IDMIL/EnchantiTouch/firmware/tsticktouch_firmware/images/kit_connection.jpg

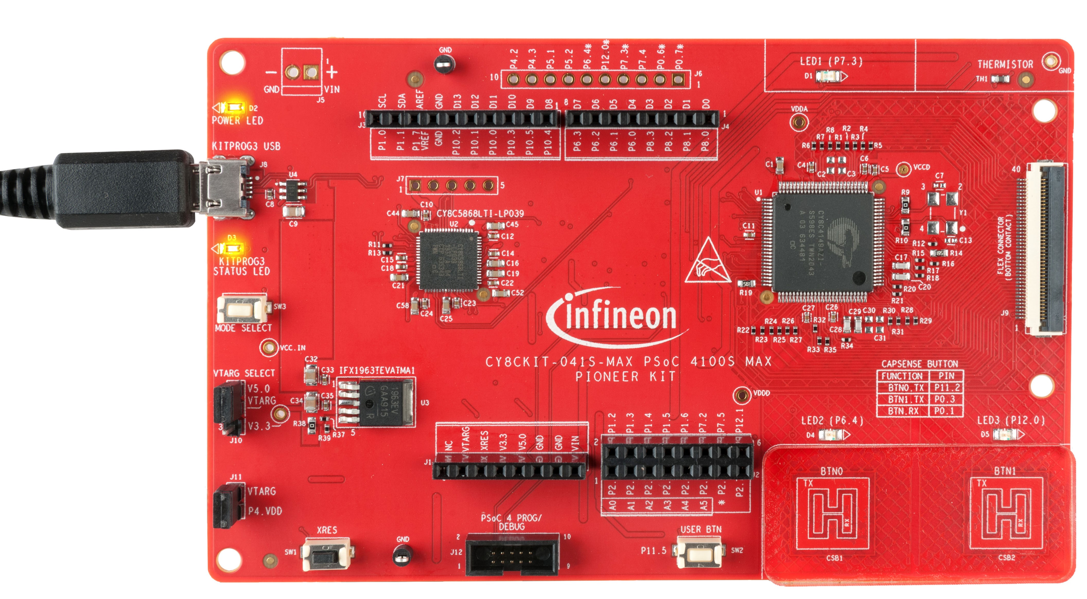
firmware/tsticktouch_firmware/images/kit_connection.jpg
