IDMIL/EnchantiTouch/firmware/tsticktouch_firmware/images/advanced-filter-settings.png

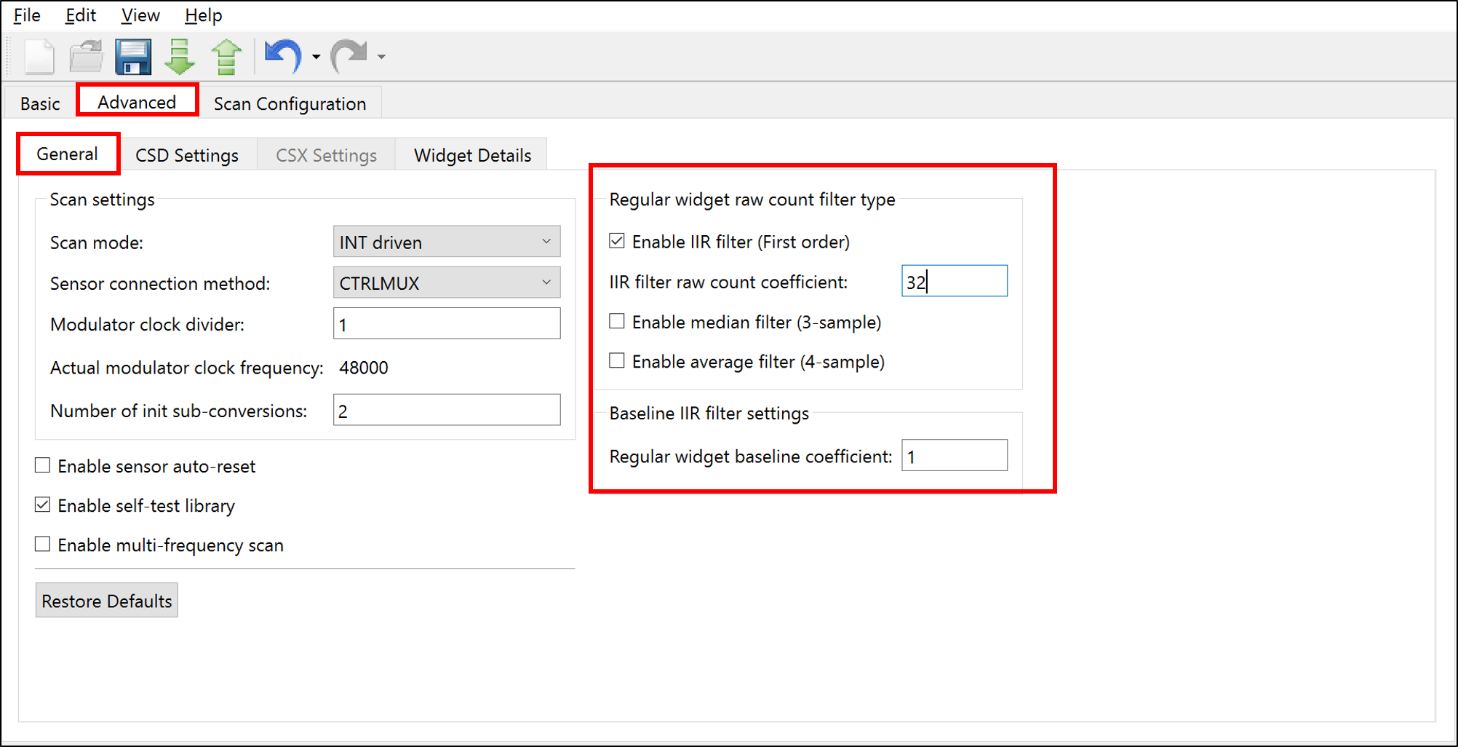
firmware/tsticktouch_firmware/images/advanced-filter-settings.png
