IDMIL/EnchantiTouch/firmware/tsticktouch_firmware/images/advanced-general-settings.png

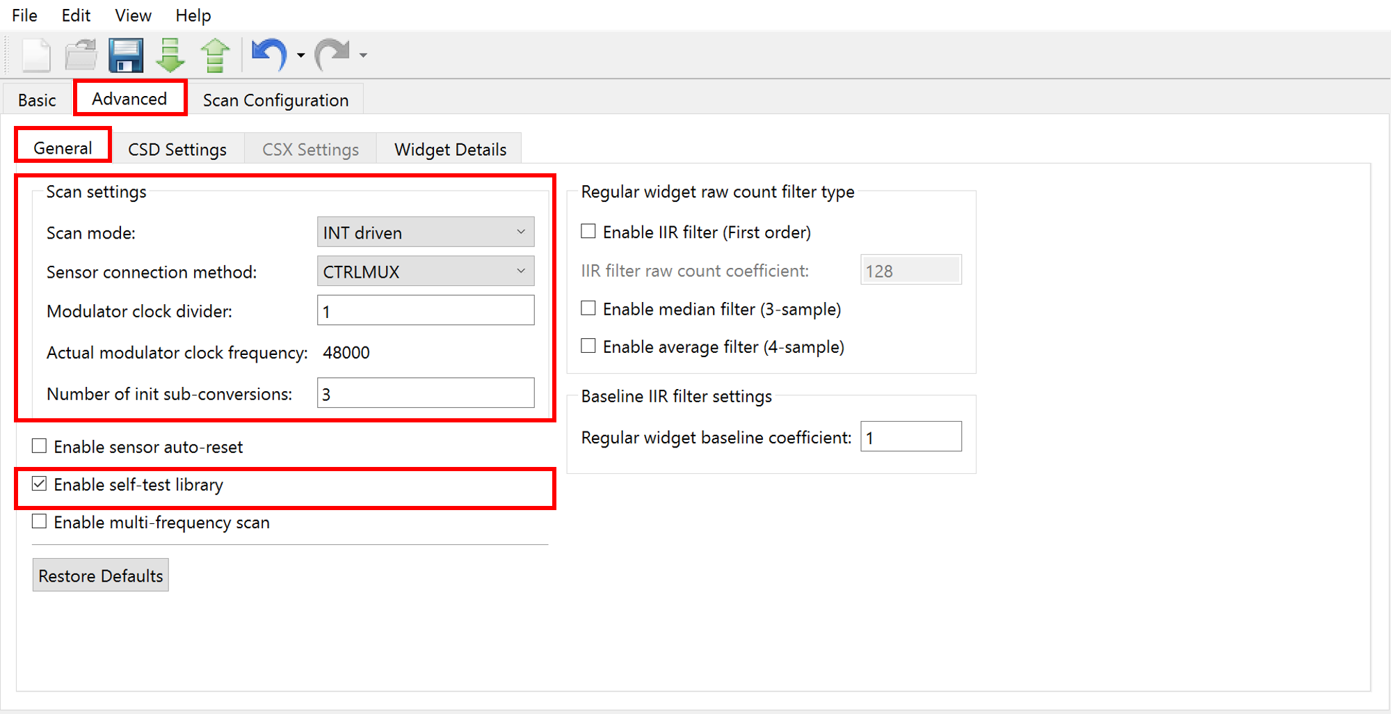
firmware/tsticktouch_firmware/images/advanced-general-settings.png
