IDMIL/EnchantiTouch/firmware/tsticktouch_firmware/images/advanced-widget-settings.png

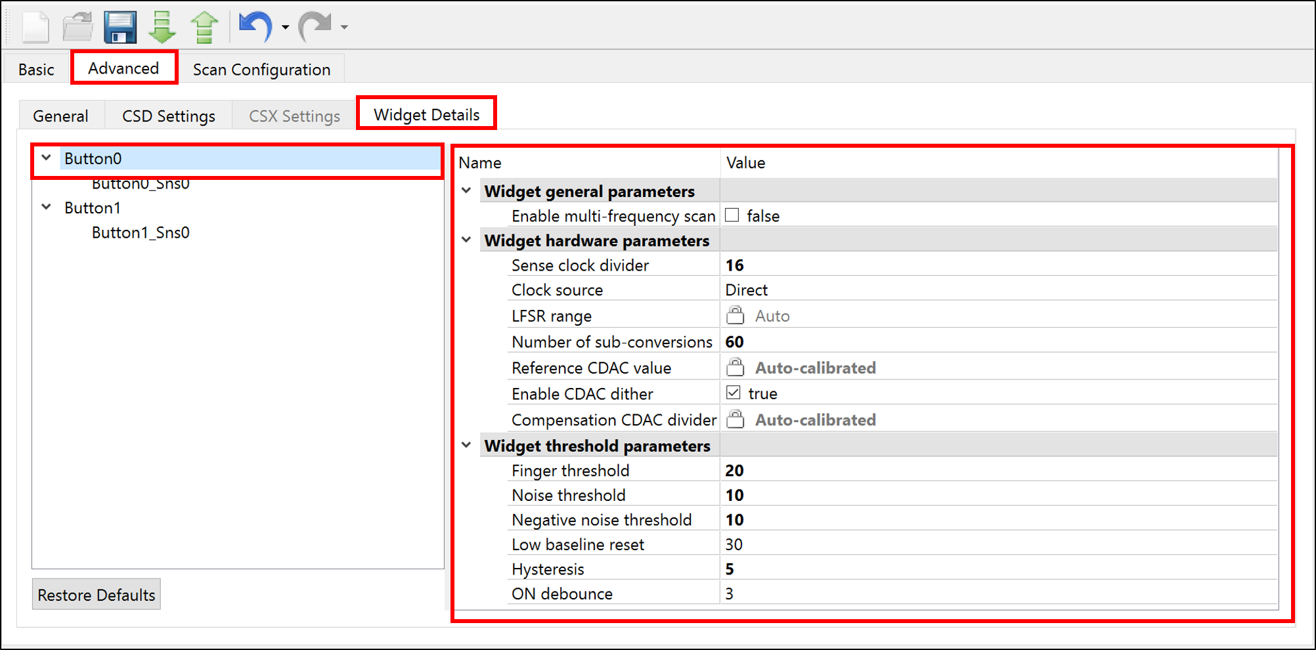
firmware/tsticktouch_firmware/images/advanced-widget-settings.png
