IDMIL/EnchantiTouch/firmware/tsticktouch_firmware/images/basic-csd-settings.png

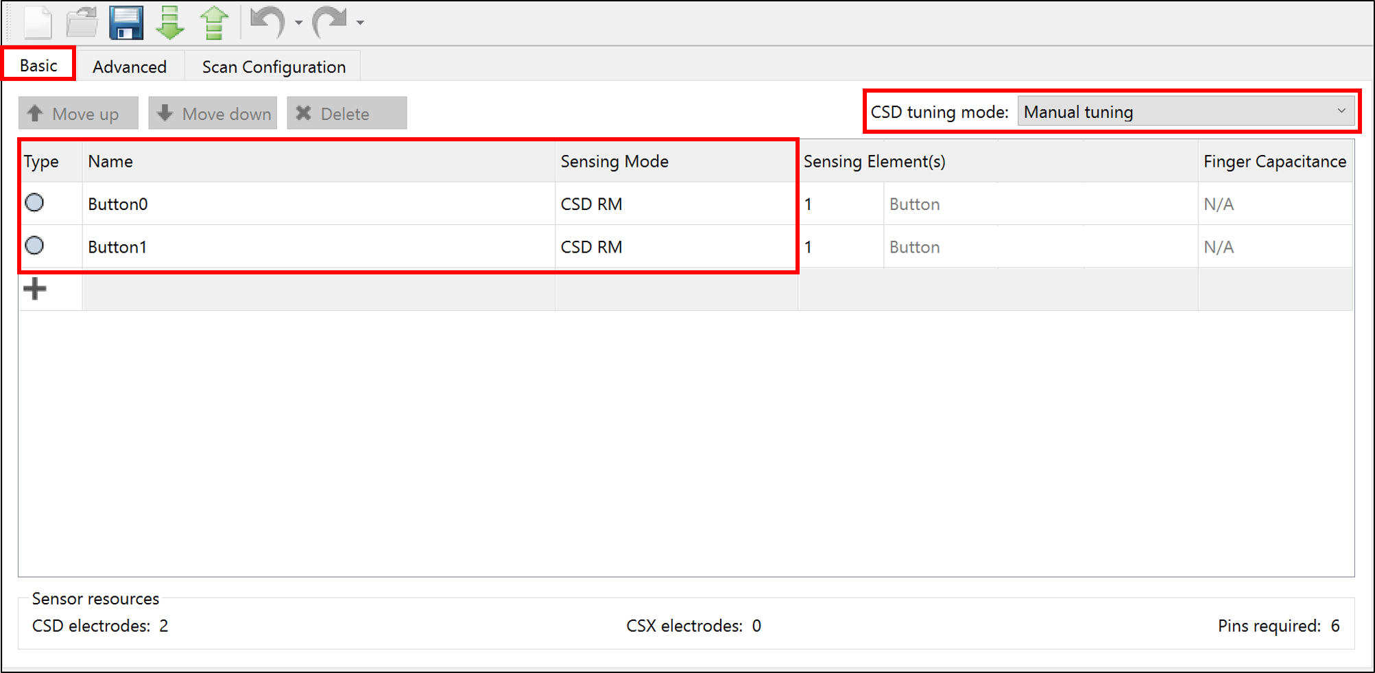
firmware/tsticktouch_firmware/images/basic-csd-settings.png
