IDMIL/EnchantiTouch/firmware/tsticktouch_firmware/images/csdrm-waveform.png

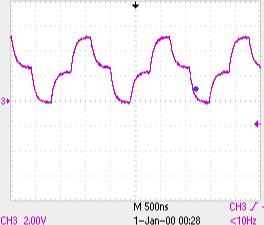
firmware/tsticktouch_firmware/images/csdrm-waveform.png
