IDMIL/EnchantiTouch/firmware/tsticktouch_firmware/images/csdrm-waveform_improper.png

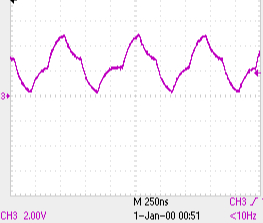
firmware/tsticktouch_firmware/images/csdrm-waveform_improper.png
