IDMIL/EnchantiTouch/firmware/tsticktouch_firmware/images/device-configurator.png

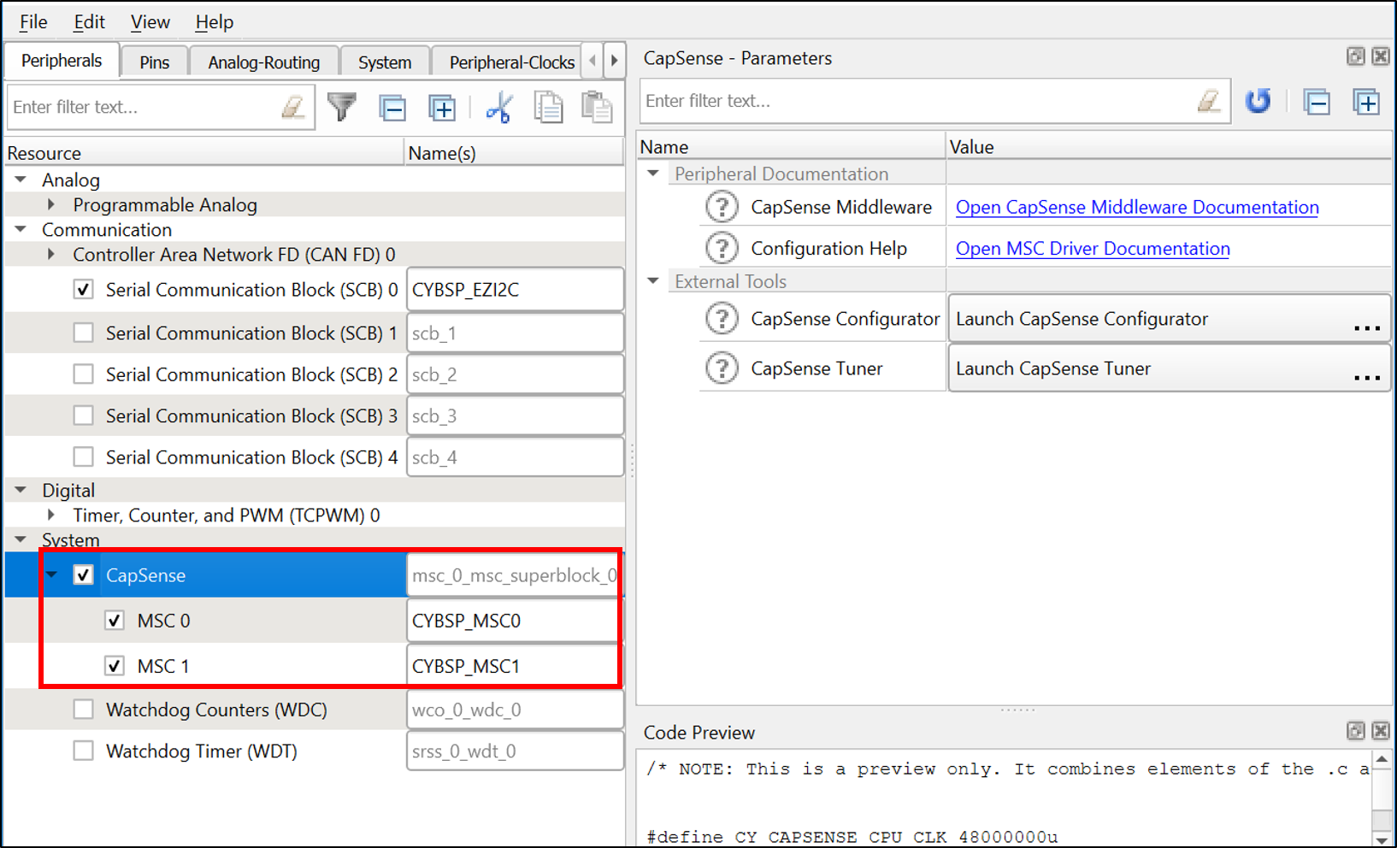
firmware/tsticktouch_firmware/images/device-configurator.png
