IDMIL/EnchantiTouch/firmware/tsticktouch_firmware/images/ezi2c-config.png

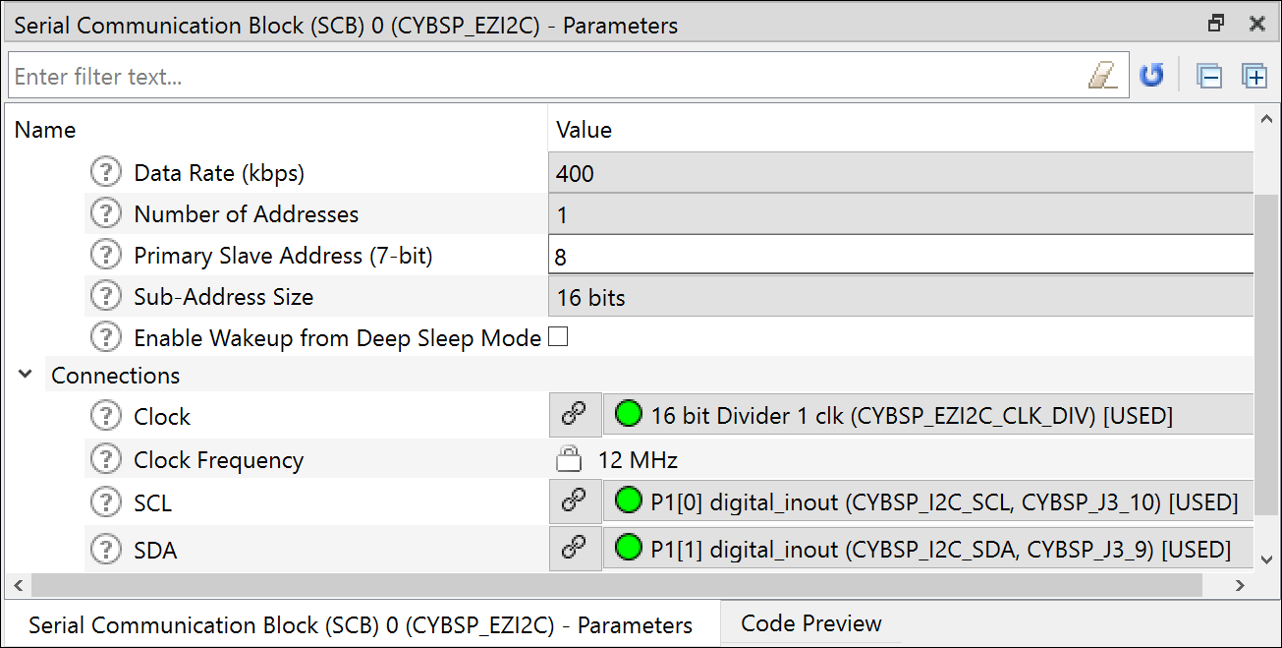
firmware/tsticktouch_firmware/images/ezi2c-config.png
