IDMIL/EnchantiTouch/firmware/tsticktouch_firmware/images/firmware-flowchart.png

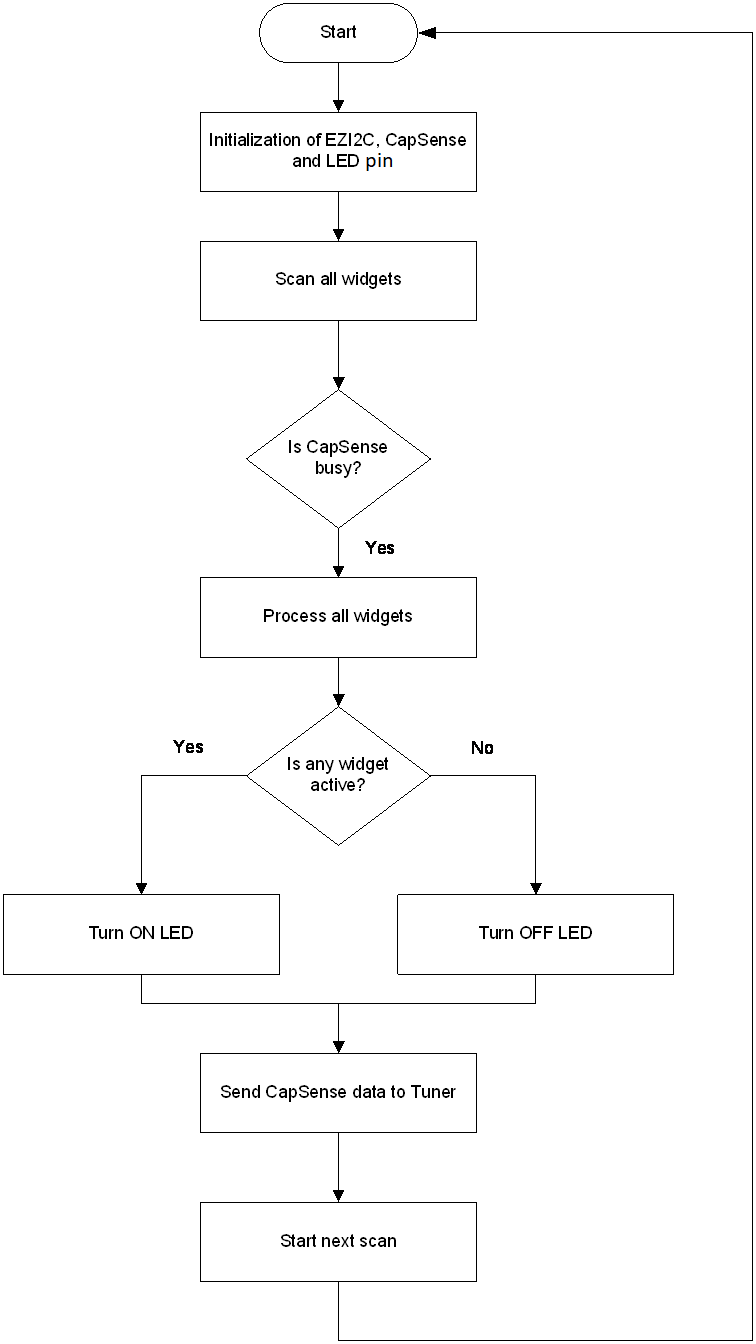
firmware/tsticktouch_firmware/images/firmware-flowchart.png
