IDMIL/EnchantiTouch/firmware/tsticktouch_firmware/images/probed-refresh-rate.png

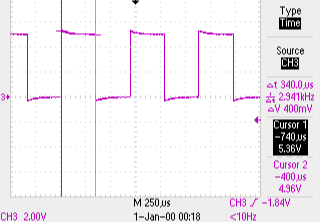
firmware/tsticktouch_firmware/images/probed-refresh-rate.png
