IDMIL/EnchantiTouch/firmware/tsticktouch_firmware/images/rawcount-equation.png

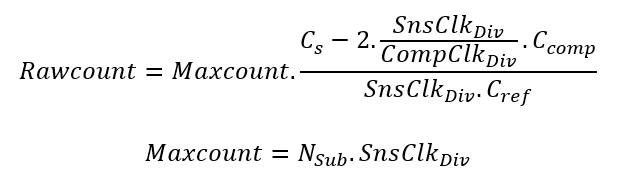
firmware/tsticktouch_firmware/images/rawcount-equation.png
