IDMIL/EnchantiTouch/firmware/tsticktouch_firmware/images/scan-configuration.png

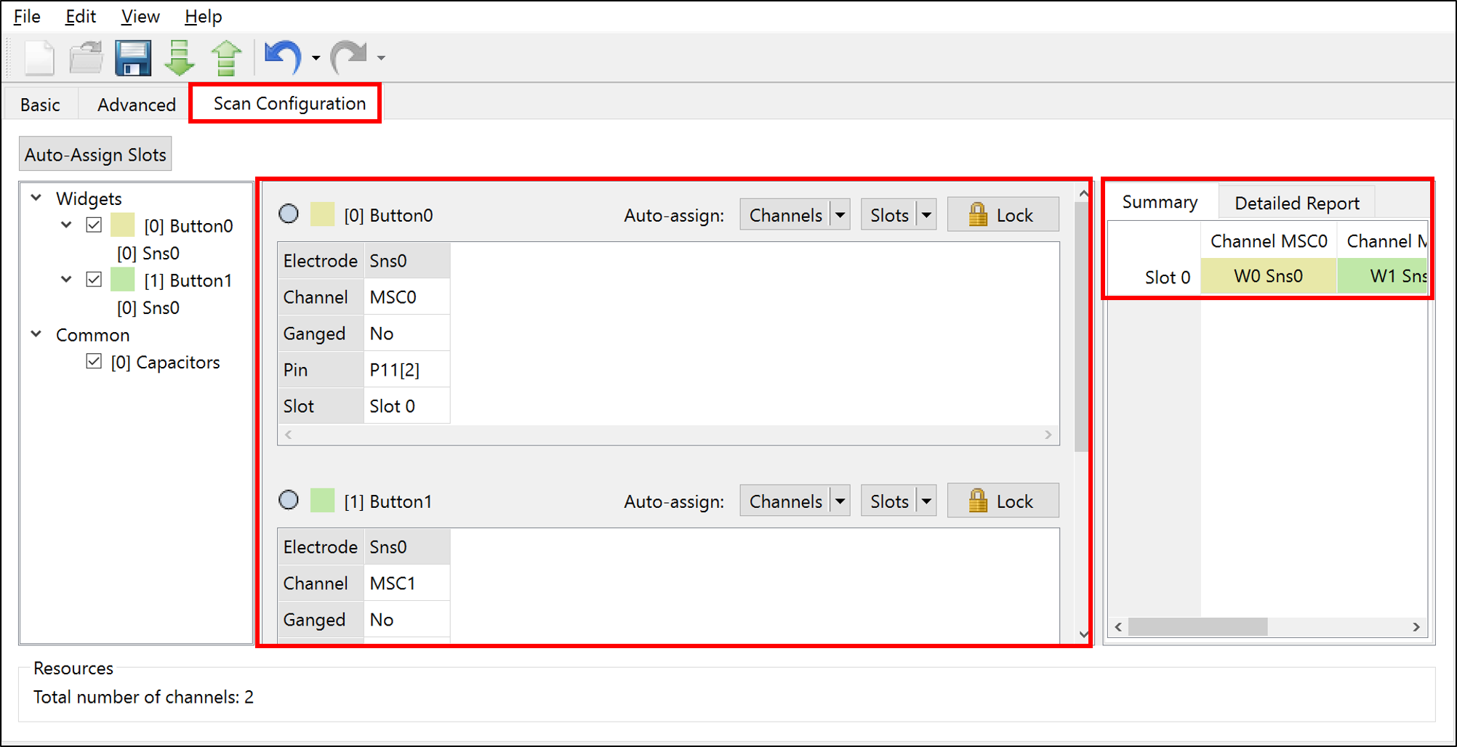
firmware/tsticktouch_firmware/images/scan-configuration.png
