IDMIL/EnchantiTouch/firmware/tsticktouch_firmware/images/tuner-acquire-noise.png

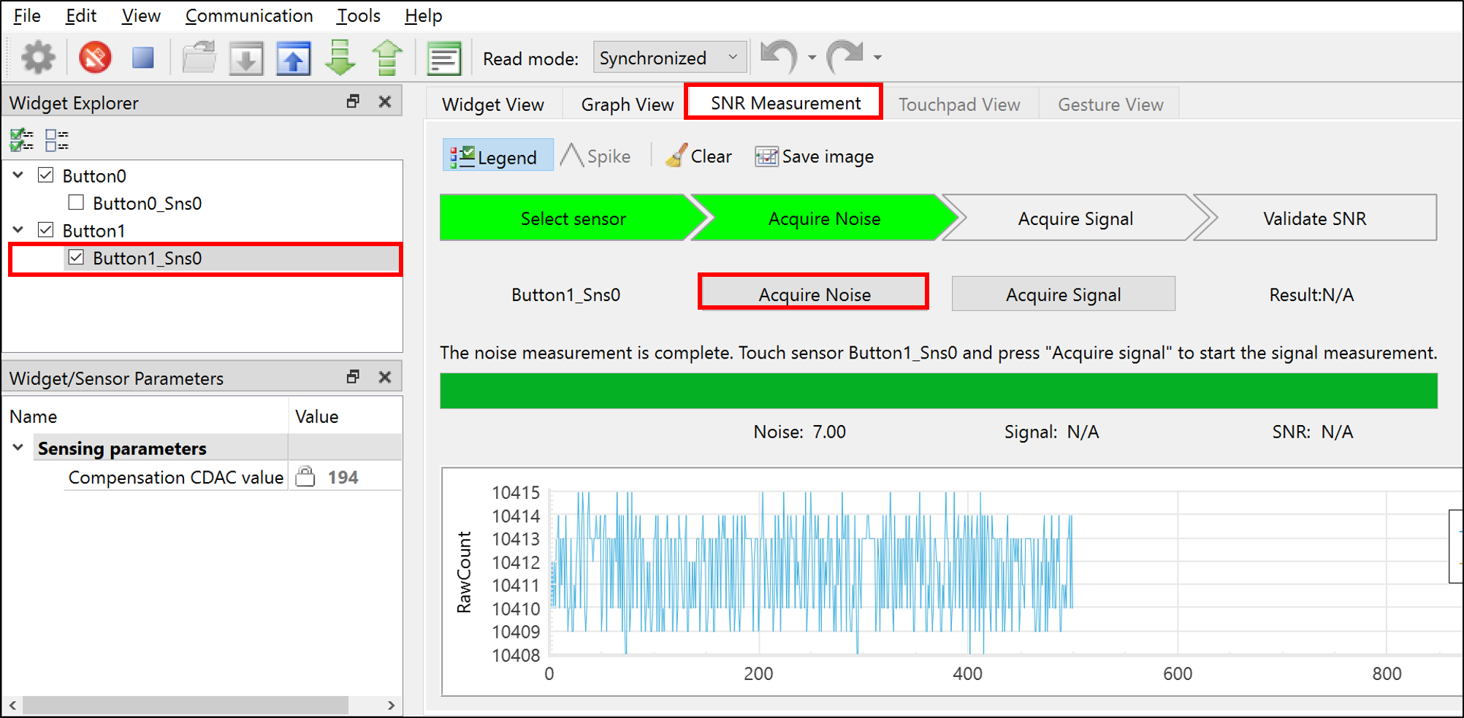
firmware/tsticktouch_firmware/images/tuner-acquire-noise.png
