IDMIL/EnchantiTouch/firmware/tsticktouch_firmware/images/tuner-cdac-setting-b0.png

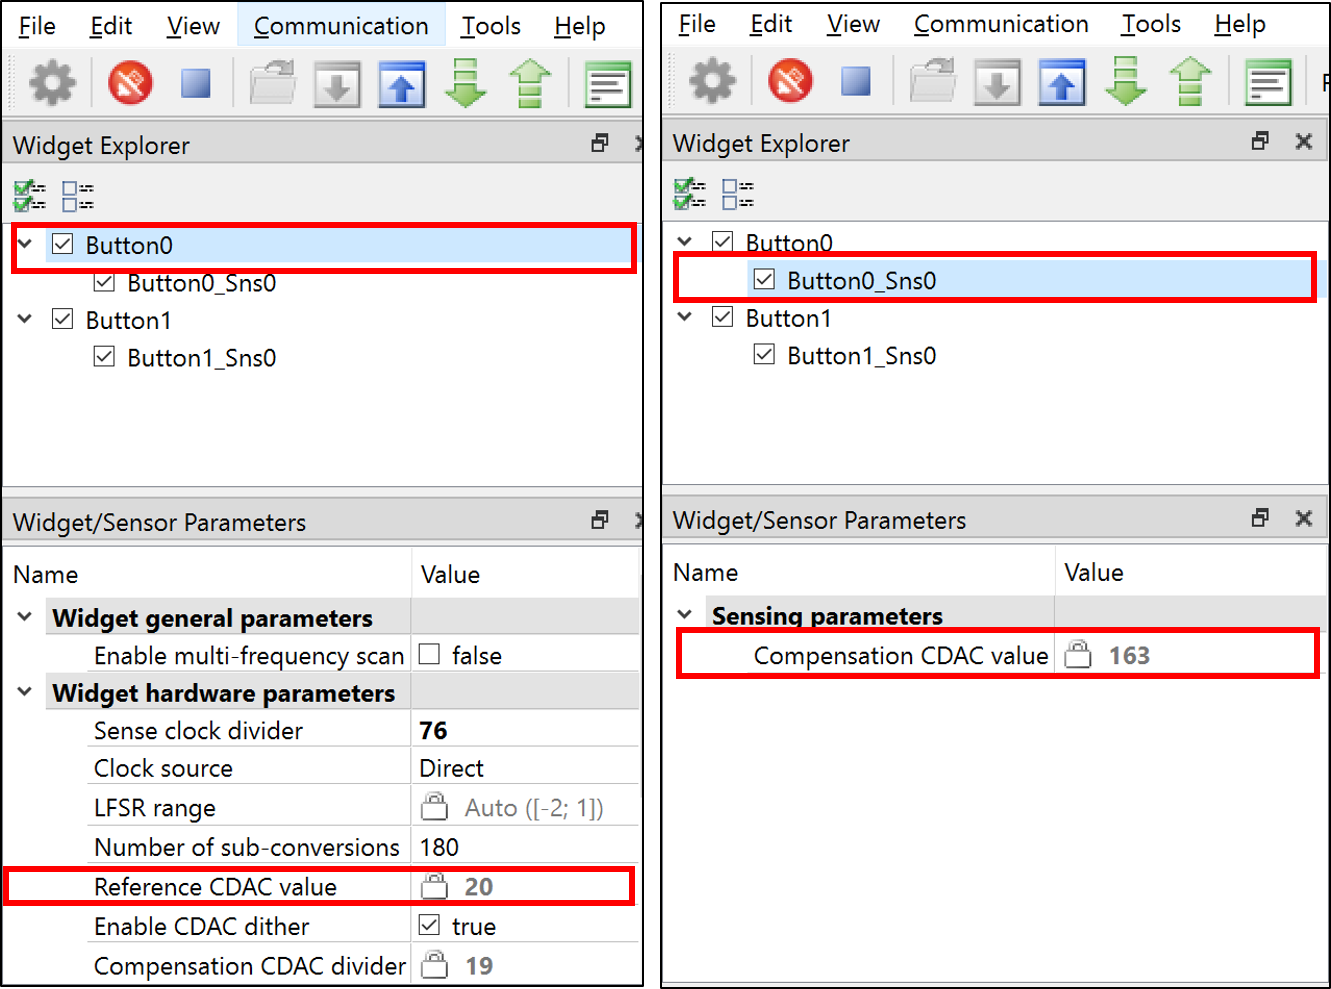
firmware/tsticktouch_firmware/images/tuner-cdac-setting-b0.png
