IDMIL/EnchantiTouch/firmware/tsticktouch_firmware/images/tuner-cdac-setting-b1.png

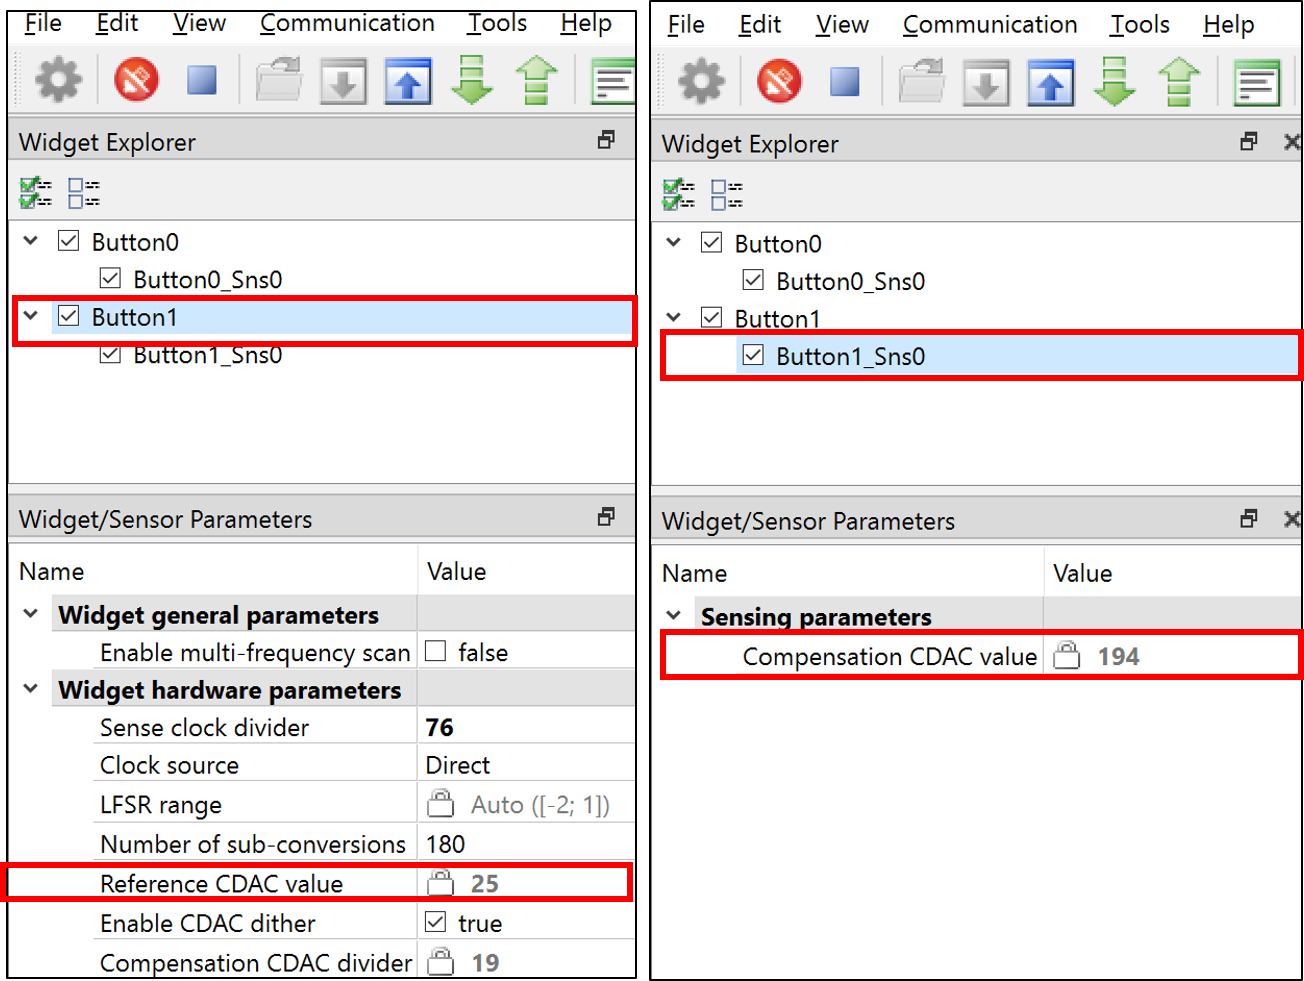
firmware/tsticktouch_firmware/images/tuner-cdac-setting-b1.png
