IDMIL/EnchantiTouch/firmware/tsticktouch_firmware/images/tuner-diff-signal.png

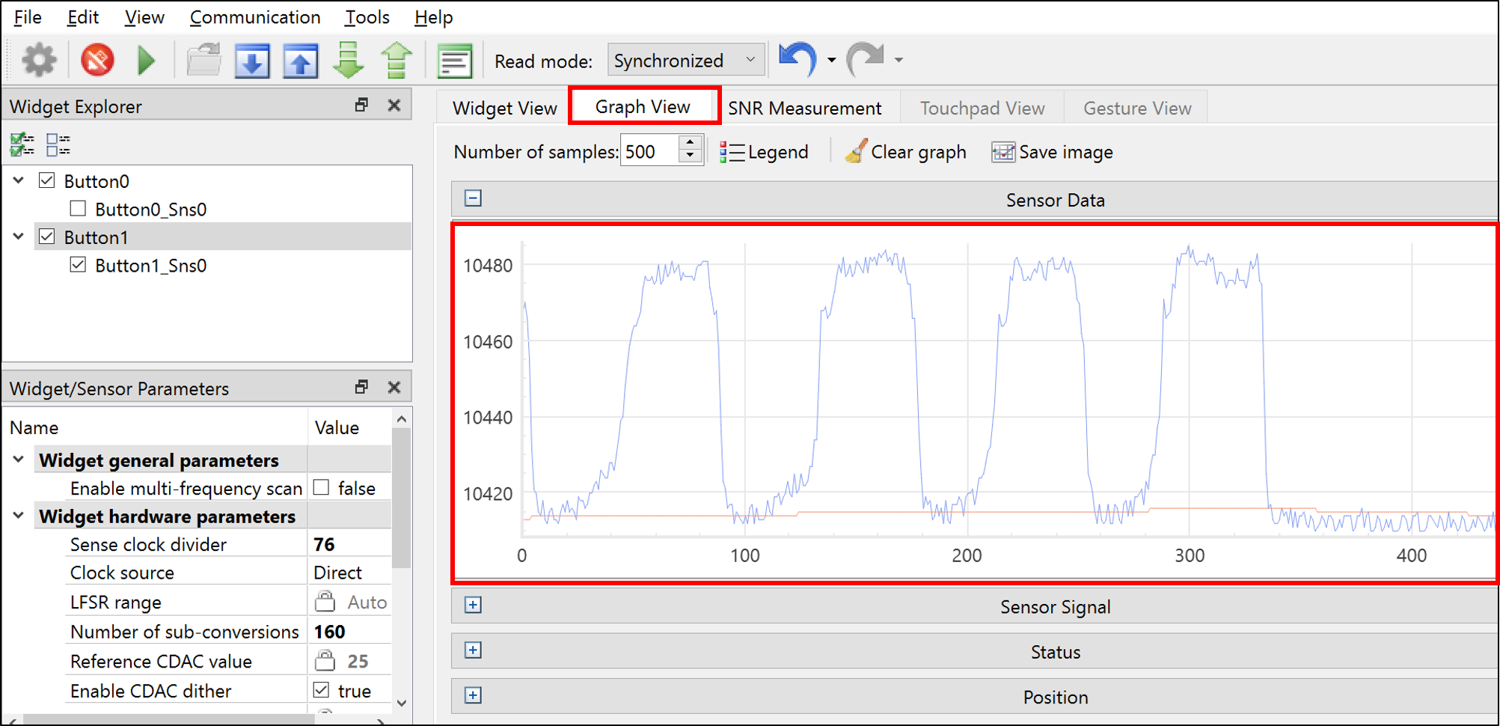
firmware/tsticktouch_firmware/images/tuner-diff-signal.png
