IDMIL/EnchantiTouch/firmware/tsticktouch_firmware/images/tuner-graph-view-intro.png

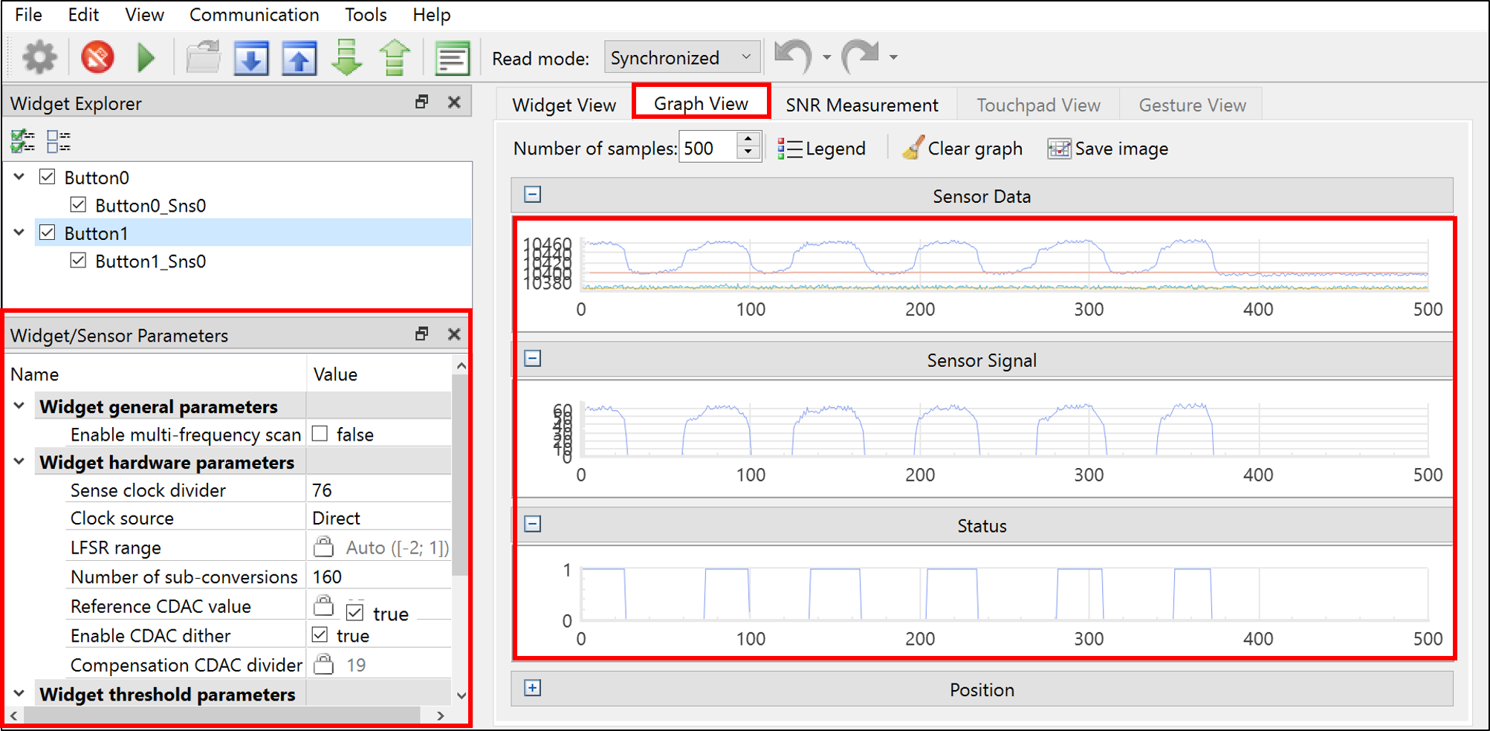
firmware/tsticktouch_firmware/images/tuner-graph-view-intro.png
