IDMIL/EnchantiTouch/firmware/tsticktouch_firmware/images/tuner-graph-view.png

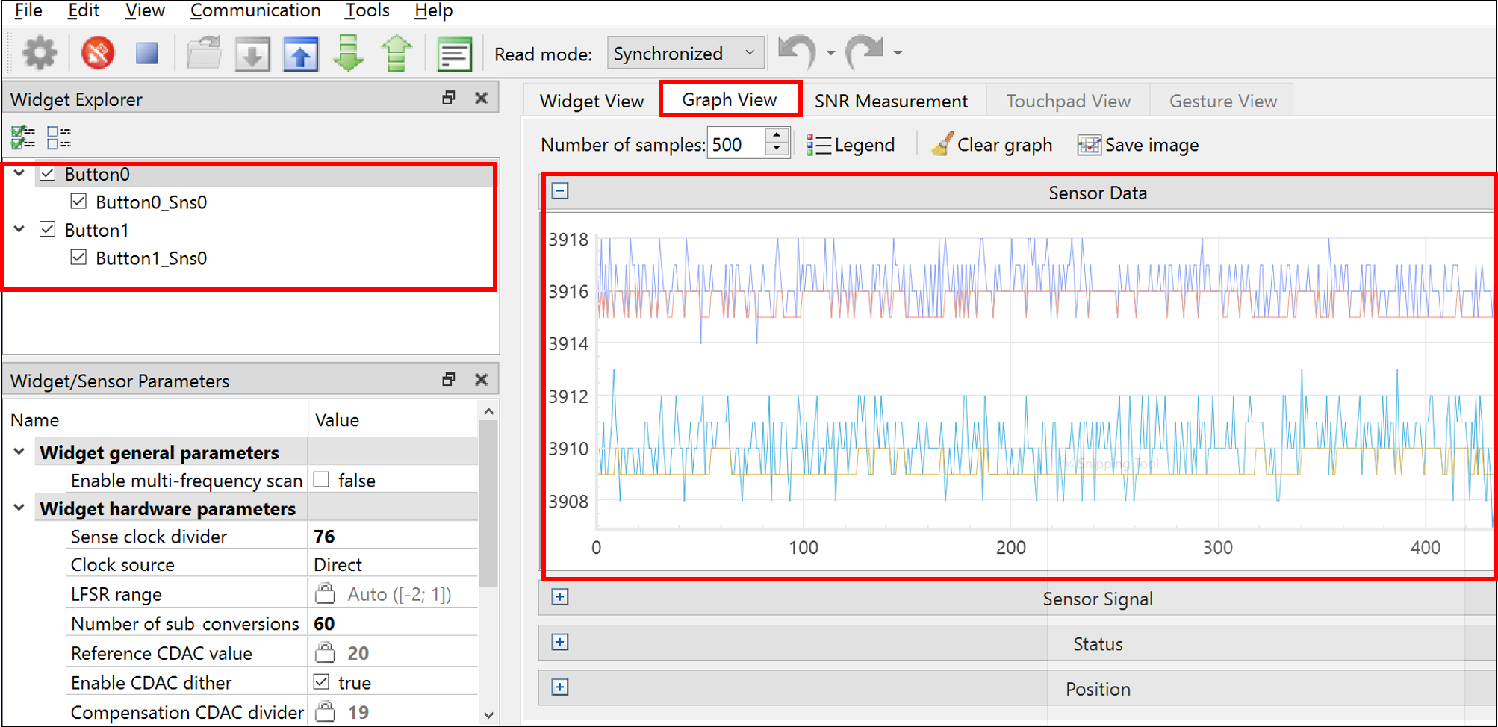
firmware/tsticktouch_firmware/images/tuner-graph-view.png
