IDMIL/EnchantiTouch/firmware/tsticktouch_firmware/images/tuner-idac-setting.png

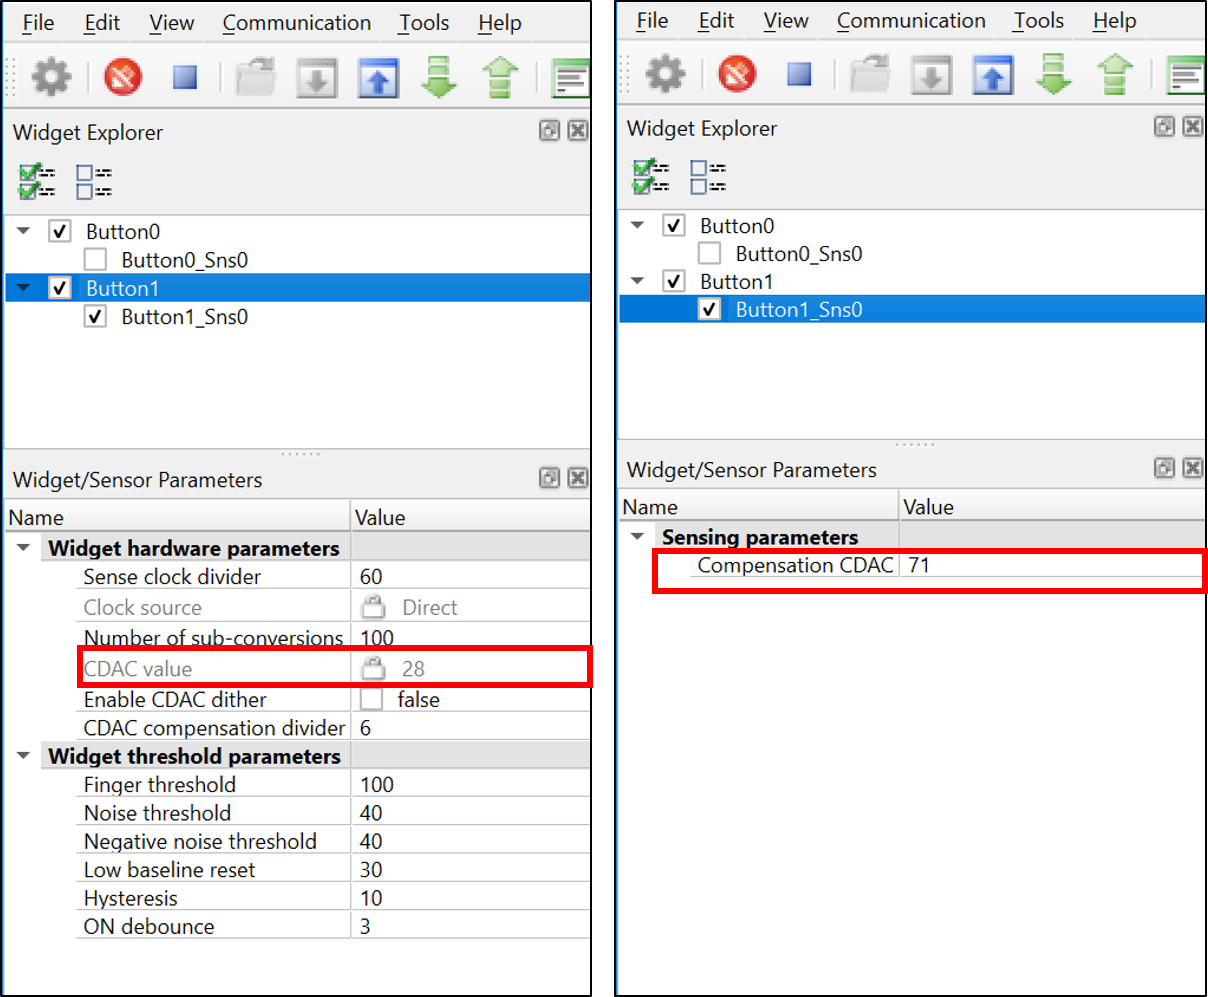
firmware/tsticktouch_firmware/images/tuner-idac-setting.png
