IDMIL/EnchantiTouch/firmware/tsticktouch_firmware/images/tuner-snr-filter.png

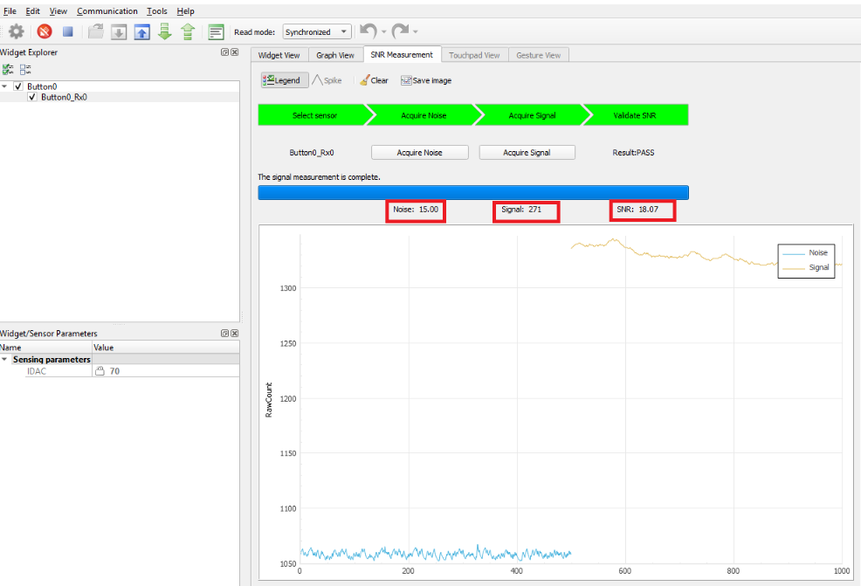
firmware/tsticktouch_firmware/images/tuner-snr-filter.png
