IDMIL/EnchantiTouch/firmware/tsticktouch_firmware/images/tuner-status.png

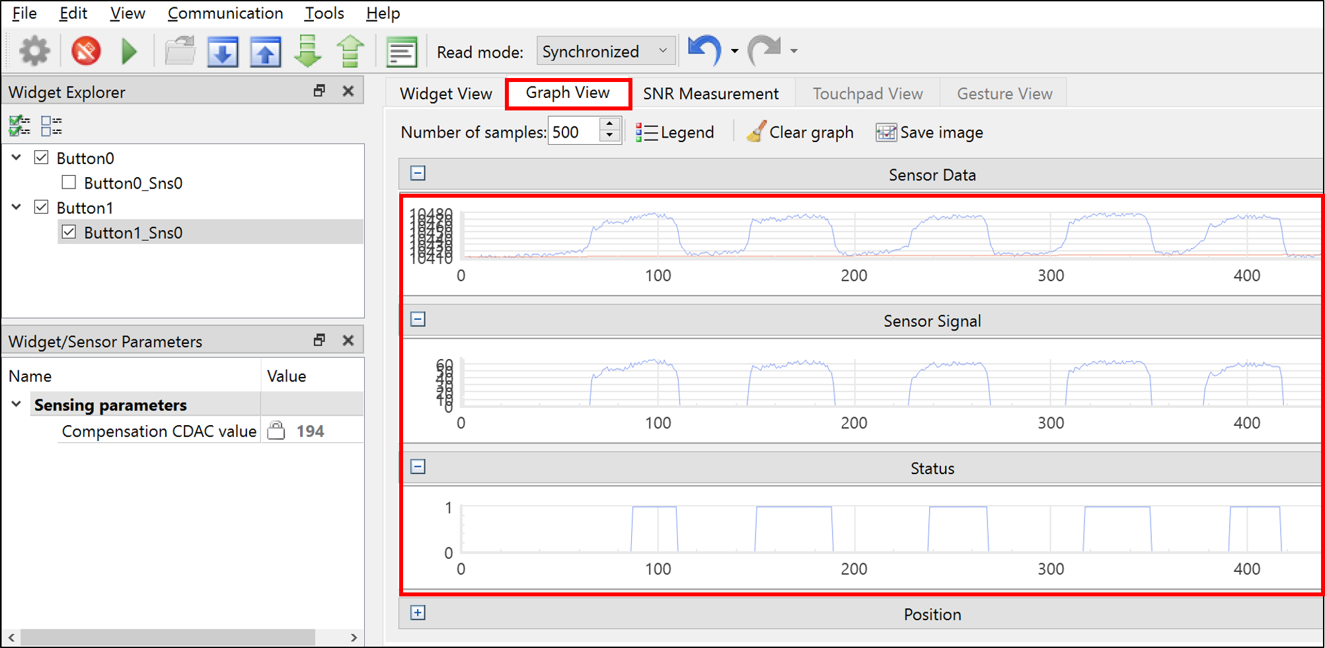
firmware/tsticktouch_firmware/images/tuner-status.png
