IDMIL/EnchantiTouch/firmware/tsticktouch_firmware/images/tuner-threshold-settings.png

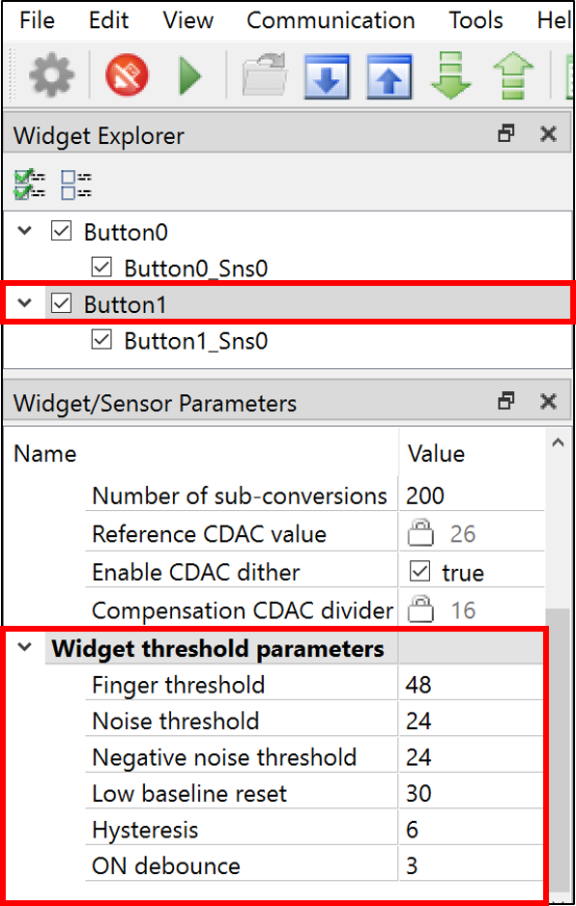
firmware/tsticktouch_firmware/images/tuner-threshold-settings.png
