IDMIL/EnchantiTouch/firmware/tsticktouch_firmware/images/tuner-widget-settings.png

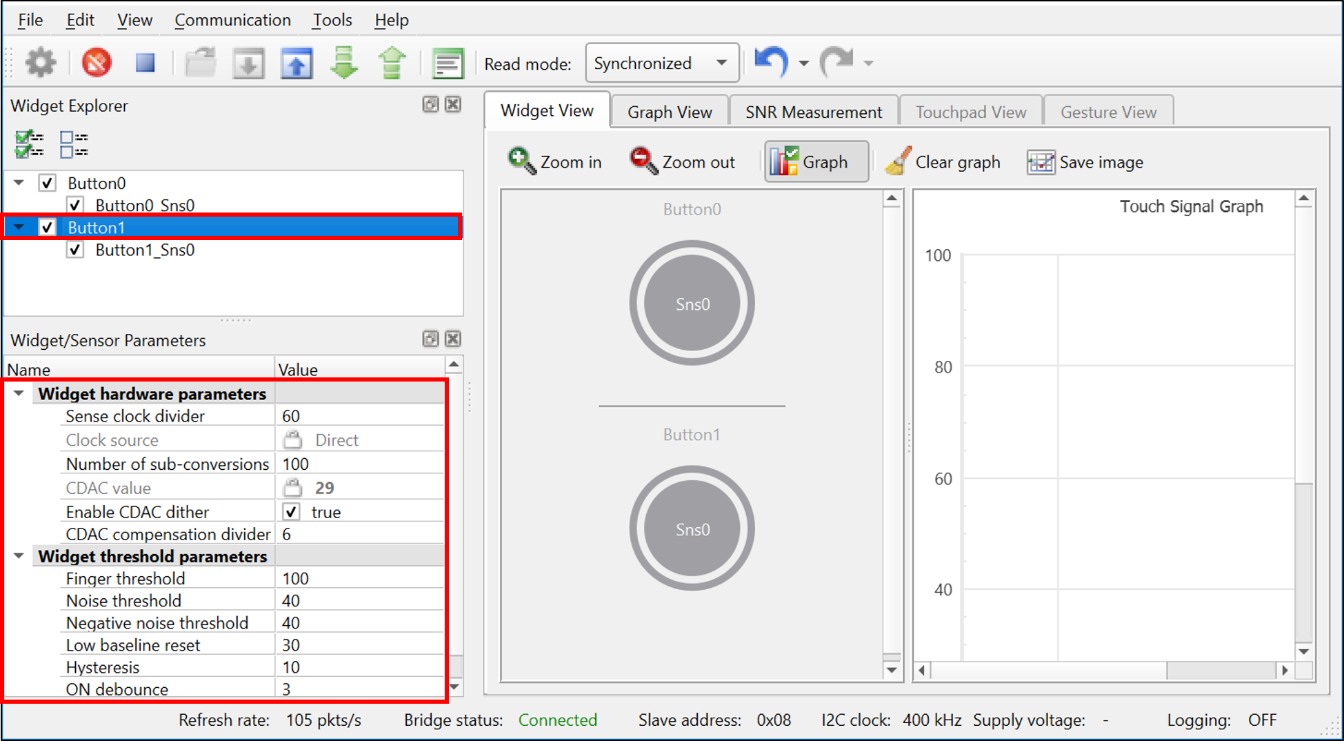
firmware/tsticktouch_firmware/images/tuner-widget-settings.png
