IDMIL/EnchantiTouch/firmware/tsticktouch_firmware/images/tuner-widget-view.png

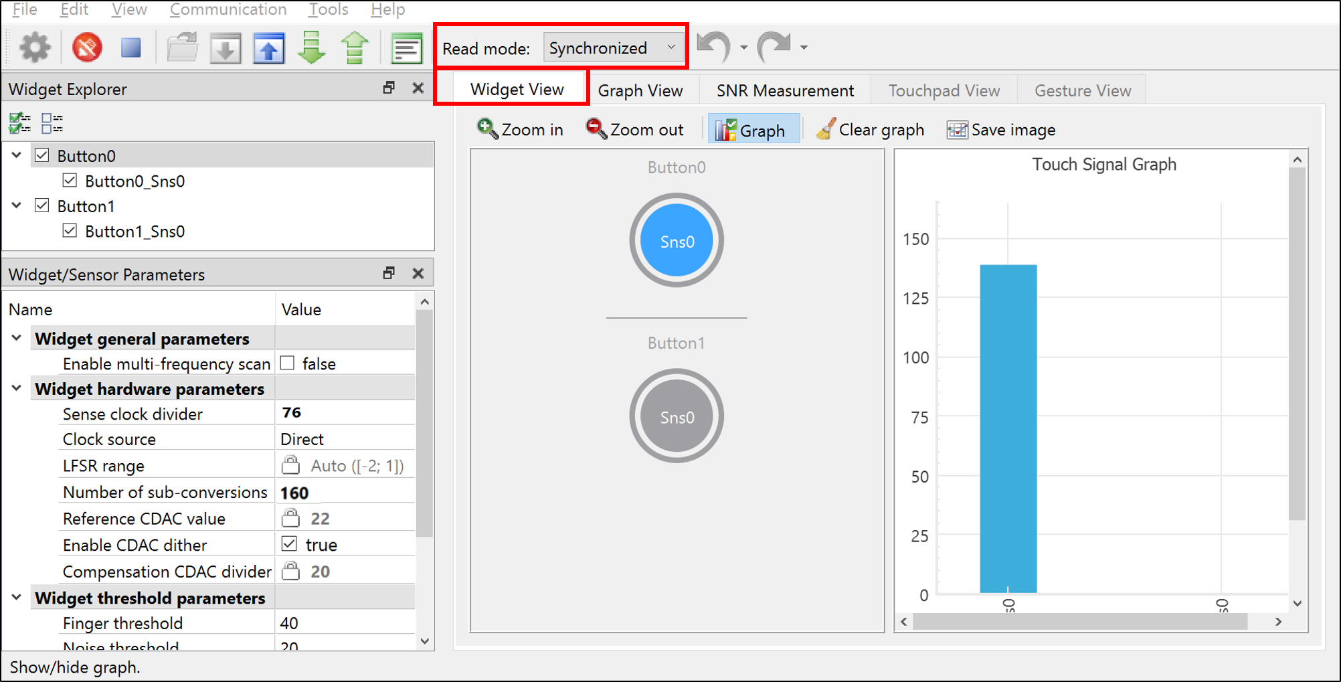
firmware/tsticktouch_firmware/images/tuner-widget-view.png
