IDMIL/EnchantiTouch/firmware/tsticktouch_firmware/images/vdda-settings.png

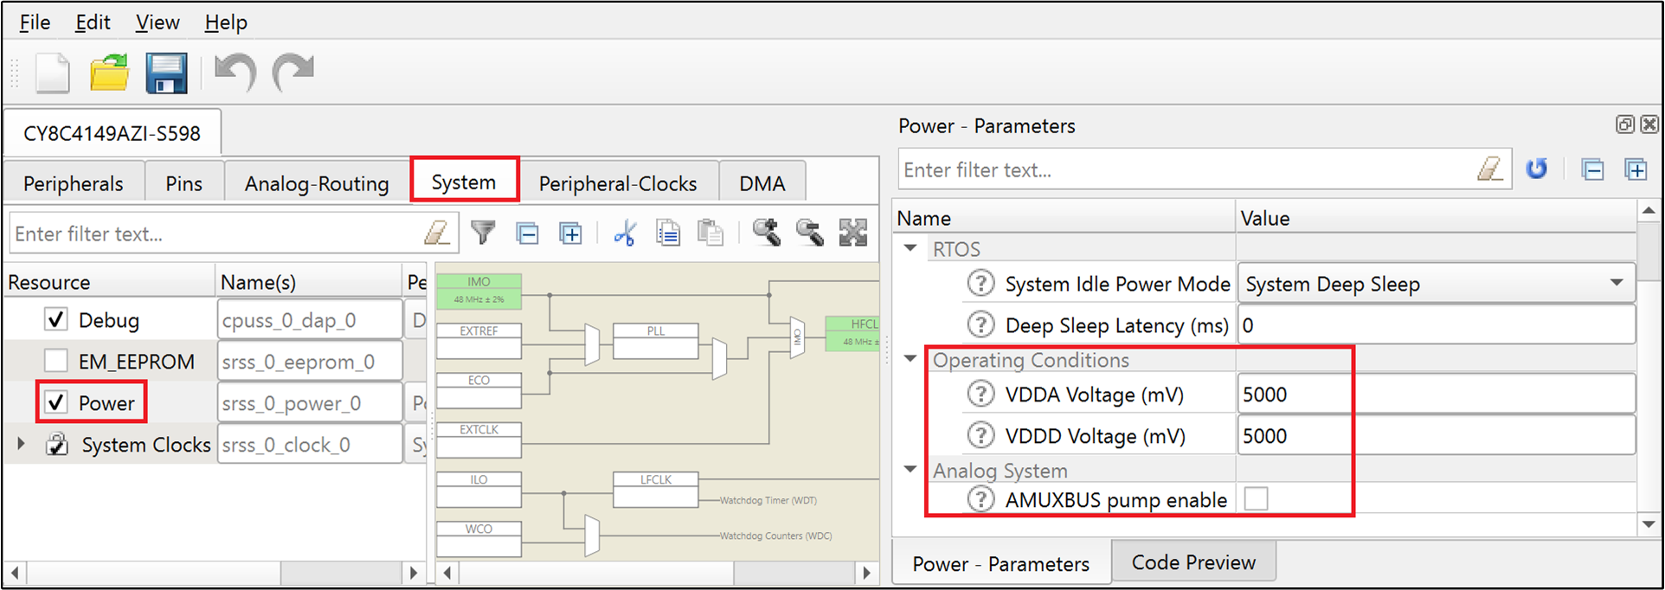
firmware/tsticktouch_firmware/images/vdda-settings.png
