IDMIL/EnchantiTouch/firmware/tsticktouch_firmware/images/tuner-comm-setup.png

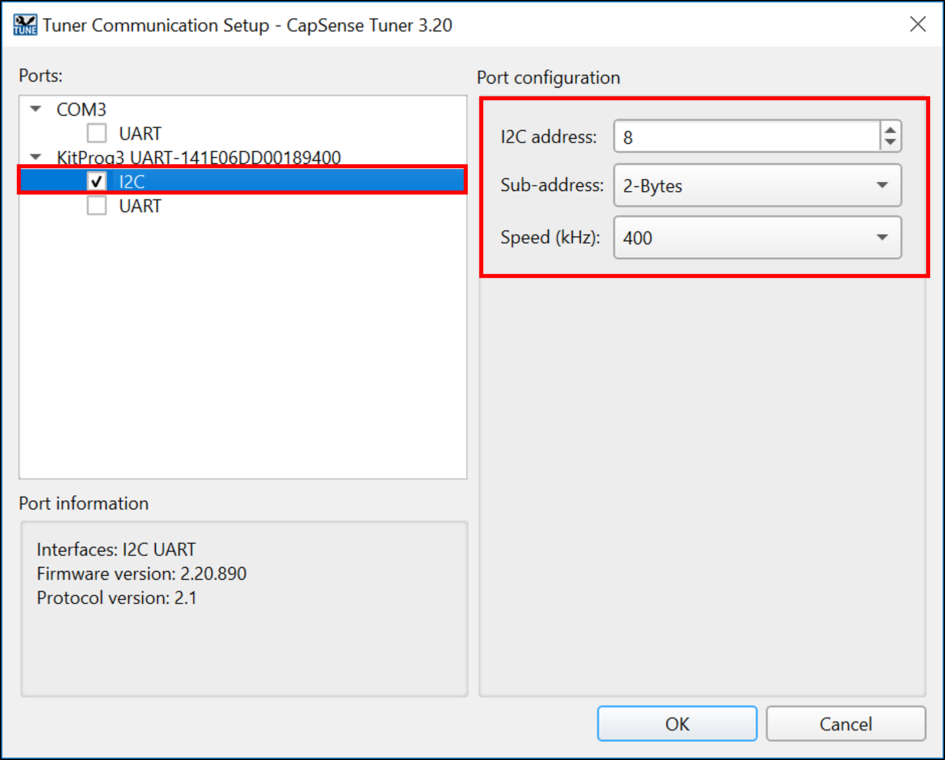
firmware/tsticktouch_firmware/images/tuner-comm-setup.png
