IDMIL/EnchantiTouch/firmware/tsticktouch_firmware/images/debug-cp-measure.png

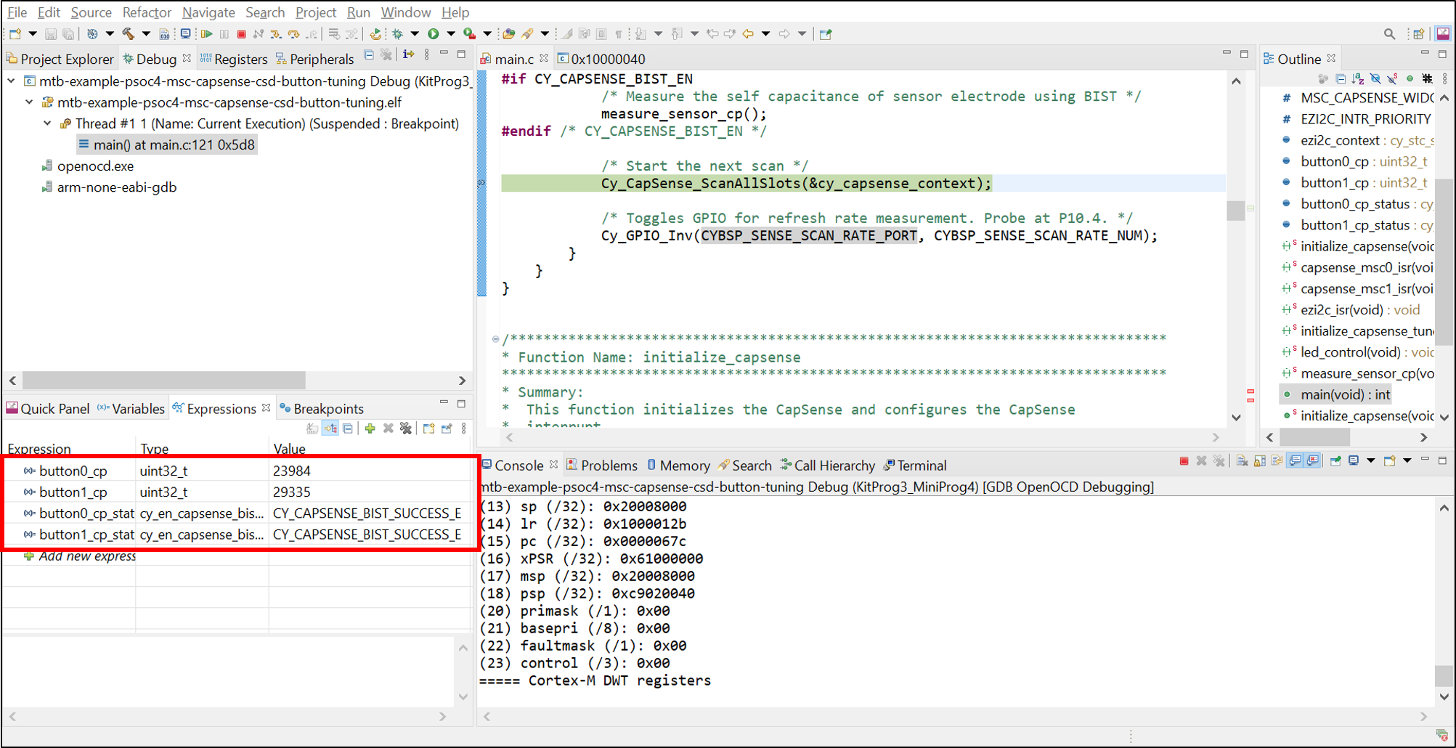
firmware/tsticktouch_firmware/images/debug-cp-measure.png
