IDMIL/EnchantiTouch/firmware/tsticktouch_firmware/images/tuning-flowchart.png

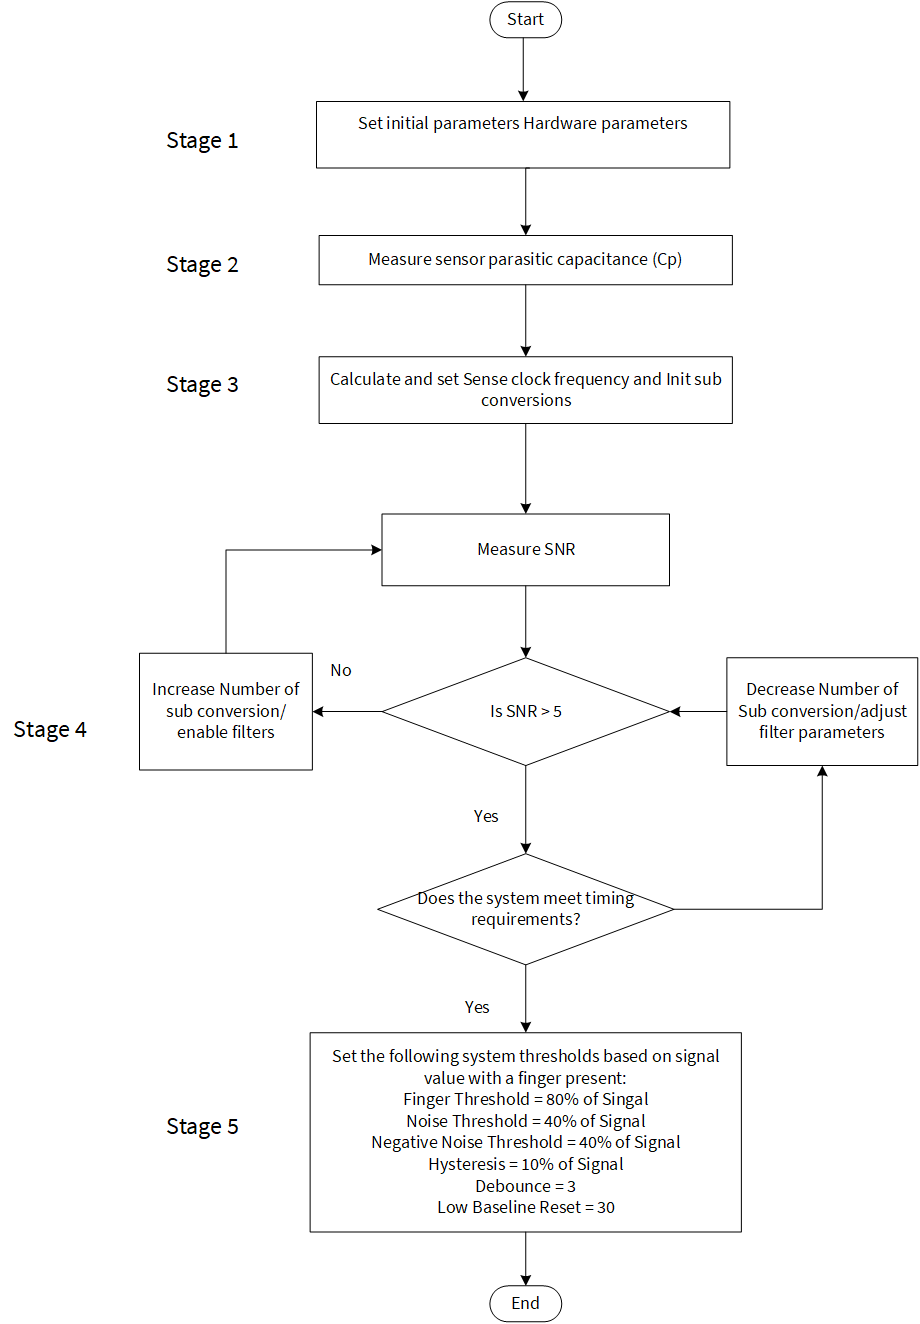
firmware/tsticktouch_firmware/images/tuning-flowchart.png
